akreager/rc-transmitter/main/touchInput.ino

// ============================================================
// touchInput.ino
// Touch state machine for resistive touchscreen
//
// Solves two problems:
// 1. Ghost-press: after a button fires or a screen changes, the
//    state machine enters WAIT_RELEASE and ignores all input
//    until the finger is physically lifted.
// 2. Noisy release: resistive touchscreens can briefly drop
//    below the pressure threshold even while held. We require
//    multiple consecutive "not pressed" readings before
//    accepting a release, preventing rapid re-triggering.
// ============================================================

// Number of consecutive "not pressed" readings required before
// we consider the finger truly lifted. Increase if you still
// see false releases on your panel.
#define RELEASE_COUNT_THRESHOLD 5

int releaseCount = 0;

void touchUpdate() {
  // tapDetected is NOT cleared here — it persists until consumed
  // by a screen update function (e.g., touch calibration).

  TSPoint p = ts.getPoint();

  // NOTE: If your touch pins are shared with other SPI/digital
  // functions, you may need to restore pin modes here:
  //   pinMode(XM, OUTPUT);
  //   pinMode(YP, OUTPUT);
  // With the pin table layout (A10/A11/D28/D29) this shouldn't
  // be necessary since they don't overlap with SPI1 pins.

  bool pressed = (p.z > MINPRESSURE && p.z < MAXPRESSURE);

  // Track consecutive not-pressed readings
  if (pressed) {
    releaseCount = 0;
  } else {
    releaseCount++;
  }

  bool released = (releaseCount >= RELEASE_COUNT_THRESHOLD);

  switch (touchState) {

    case TOUCH_IDLE:
      if (pressed) {
        // Check debounce timer
        unsigned long now = millis();
        if (now - lastTouchTime < TOUCH_DEBOUNCE_MS) {
          // Too soon after last press, ignore
          break;
        }

        touchState = TOUCH_PRESSED;
        lastTouchTime = now;

        // Store raw values first (needed by touch calibration)
        rawTouchX = p.x;
        rawTouchY = p.y;

        // Set tap flag (consumed by calibration or other listeners)
        tapDetected = true;

        // Map to screen coordinates
        mapTouchCoords(p);

        // Fire button check on this single frame
        processTouch(touchX, touchY);
      }
      break;

    case TOUCH_PRESSED:
      // Transition: finger still down = held, finger up = idle
      if (released) {
        touchState = TOUCH_IDLE;
      } else {
        touchState = TOUCH_HELD;
      }
      break;

    case TOUCH_HELD:
      if (released) {
        touchState = TOUCH_IDLE;
      }
      // Future: long-press detection could go here by tracking
      // how long we've been in HELD state.
      break;

    case TOUCH_WAIT_RELEASE:
      // Eat all input until finger is fully lifted.
      // This is the key to preventing ghost presses on screen
      // transitions -- no new press can register until the
      // physical touch ends AND stays ended for several frames.
      if (released) {
        touchState = TOUCH_IDLE;
      }
      break;
  }
}

void mapTouchCoords(TSPoint &p) {
  // Map raw resistive values to pixel coordinates.
  // Uses runtime calibration variables (updated by touch cal routine).
  // Rotation 2 = 180° from default, so axes are inverted.
  touchX = map(p.x, tsMinX, tsMaxX, SCREEN_W, 0);
  touchY = map(p.y, tsMinY, tsMaxY, SCREEN_H, 0);

  // Clamp to screen bounds
  touchX = constrain(touchX, 0, SCREEN_W - 1);
  touchY = constrain(touchY, 0, SCREEN_H - 1);
}

// Call this after any action that should block further input
// until the finger is lifted (button press, screen change, etc.)
void requireRelease() {
  touchState = TOUCH_WAIT_RELEASE;
  releaseCount = 0;
}
