akreager/rc-transmitter/test_sketches/txHello/txHello.ino

/*
  Arduino Wireless Communication Tutorial
      Example 1 - Transmitter Code

  by Dejan Nedelkovski, www.HowToMechatronics.com

  Library: TMRh20/RF24, https://github.com/tmrh20/RF24/
*/

#include <SPI.h>
#include <nRF24L01.h>
#include <RF24.h>

RF24 radio(9, 10); // CE, CSN

const byte address[6] = "00001";

void setup() {
  radio.begin();
  radio.openWritingPipe(address);
  radio.setPALevel(RF24_PA_MIN);
  radio.stopListening();
}

void loop() {
  const char text[] = "Hello World";
  radio.write(&text, sizeof(text));
  delay(1000);
}
